btpv/adaline/Elastomer_Trellis.jpg

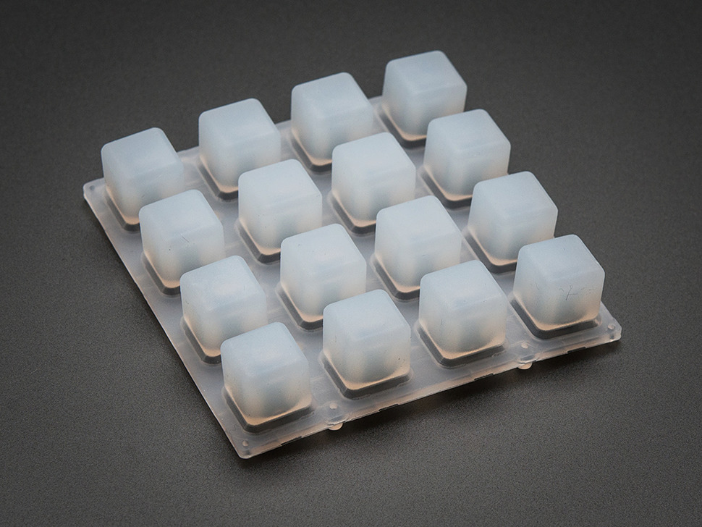
Elastomer_Trellis.jpg
